jasonacox/Powerwall-Display/PW-Display.kicad_sch

## KiCad design PW-Display.kicad_sch (2022-01-23)

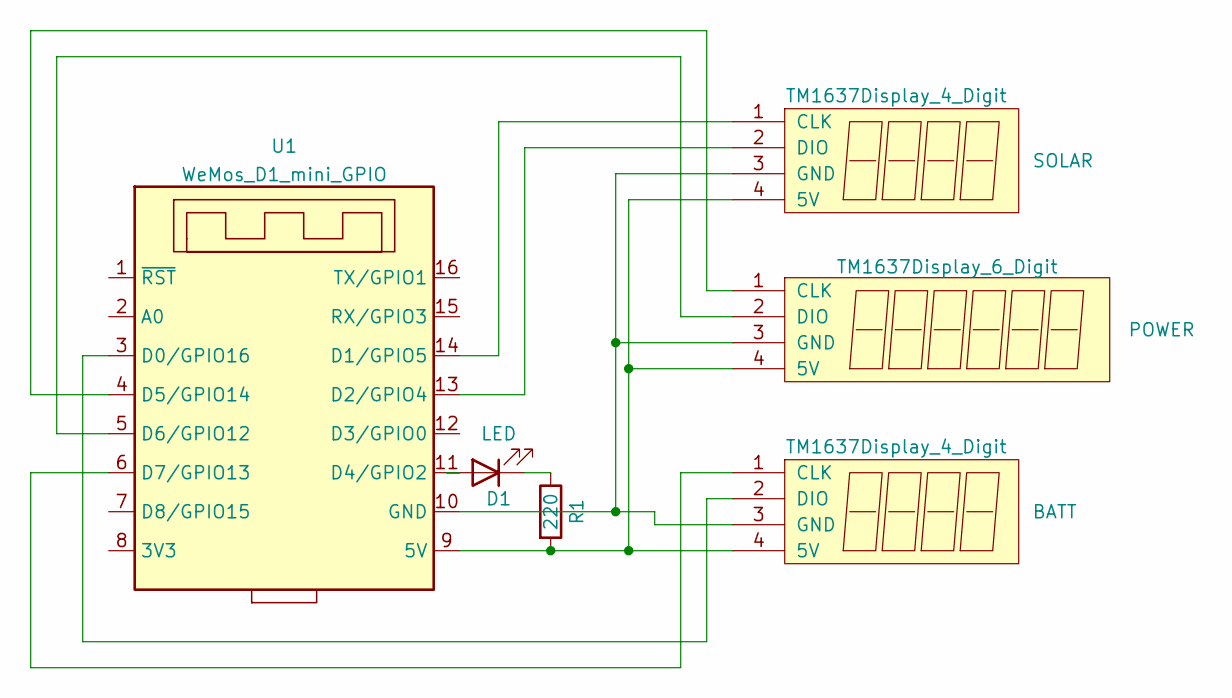
[picture p5: schematic PW-Display.kicad_sch]

Parts:
BATT: TM1637Display_4_Digit
D1: LED
POWER: TM1637Display_6_Digit
R1: 220
SOLAR: TM1637Display_4_Digit
U1: WeMos_D1_mini_GPIO; WEMOS_D1_mini_light

Connections:
unnamed: BATT.1 (CLK), U1.6 (D7/GPIO13)
unnamed: BATT.2 (DIO), U1.3 (D0/GPIO16)
unnamed: BATT.3 (GND), POWER.3 (GND), SOLAR.3 (GND), U1.10 (GND)
unnamed: BATT.4 (5V), POWER.4 (5V), R1.2, SOLAR.4 (5V), U1.9 (5V)
unnamed: D1.1 (K), R1.1
unnamed: D1.2 (A), U1.11 (D4/GPIO2)
unnamed: POWER.1 (CLK), U1.4 (D5/GPIO14)
unnamed: POWER.2 (DIO), U1.5 (D6/GPIO12)
unnamed: SOLAR.1 (CLK), U1.14 (D1/GPIO5)
unnamed: SOLAR.2 (DIO), U1.13 (D2/GPIO4)
